nbroeking/Apollo/SongListener/src/Application.cpp

#include "ScopedLock.h"
#include "Event.h"
#include "Log.h"
#include "Application.h"
#include <fftw3.h>
#include <cstring>
#include <math.h>
#include <unistd.h>
#include "Processor.h"
using namespace std;

//Main Running Loop
int MainApplication::run()
{
	//No two threads can try and run the application at a time. It shouldn't
	// happen anyway but you never know what mistakes i will make.
	isRunning = true;
	
    if (!(s = pa_simple_new(NULL, "Song Listener", PA_STREAM_RECORD, NULL, "record", &ss, NULL, NULL, &error))) {
        fprintf(stderr, __FILE__": pa_simple_new() failed: %s\n", pa_strerror(error));
        return 2;
    }
	while (shouldRun.load())
	{
	    int16_t buf[BUFSIZE];
       
        
        //Record some data ...
        if (pa_simple_read(s, buf, sizeof(buf), &error) < 0) {
            fprintf(stderr, __FILE__": pa_simple_read() failed: %s\n", pa_strerror(error));
            return 3;
        }
 
        //THis is a bad check so we only do the fft on real data
        if( buf[0] != 0){
           
            //Combining the left and right streams
           for( int i = 0; i < INSIZE; i++){
                int16_t left = buf[i*2];
                int16_t right = buf[i*2 +1];

                in[i] = ((float)left + (float)right) / 65536.f;
            }

            //Windowing I think 
            for( int i =0; i < INSIZE; i++){
                //in[i] = buf[i];
                in[i] *= 0.54f - 0.46f * cosf( (3.1415926 * 2.f * i) / (BUFSIZE - 1) ); 
            }


            fftw_execute(p);

            // I rewrite to out[i][0] squared absolute value of a complex number out[i].
            //int step = MAXFREQ/OUTPUTSIZE;
            int steps = 1;

            int integral = 0;
            
            // cerr << "Values"<< endl;
            for (int i = 0; i < MAXANALYZE; ++i)
            {
                double value = out[i][0]*out[i][0] + out[i][1]*out[i][1];
                integral += value;
                //out[i][0] = 10*log(value);
                //out[i][0] = 10*log(value);
                out[i][0] = value;
                //cerr << steps*step << ", " << out[i][0]<< endl;
                steps+=1;
            }
            
            //ncerr << "Intgral, "<< integral << endl;           

            //exit(0);
            int8_t  bitmask[8];

            processor.process(out, MAXANALYZE, bitmask,integral);


            /*cout << "Bitmask" << endl;

            for( int i =0; i < 8; i++){
                printf(" 0x%02X ", bitmask[i] );
            }
            cout << endl;
            */
            if( arduino){
                fwrite(bitmask , sizeof(char), 8, arduino);
            }
            fflush(arduino);
          
             
            //exit(0);
        }
    }

	isRunning = false;

    printf("LIGHTD: Application Exiting Normally\n");
	return 0;
}

//Constructor
MainApplication::MainApplication(){
	isRunning = false;
	shouldRun.store(true);

    arduino = NULL;

    //Oh gods of programming Im sorry for this polling law break
    int retries = 0;
    while(access ("/dev/ttyACM0", F_OK) != 0)
    {
        fprintf(stderr, "Could not find the arduino trying again in 3 seconds\n");
        sleep(3);
        retries += 1;

       if( retries > 10){
            shouldRun.store(false);
            break;
        }
    }
    
   
    arduino = fopen("/dev/ttyACM0", "w");

    s = NULL;
   
   for (int i = 0; i < BUFSIZE; ++i){
        in[i] = 0.f;
    }
   for (int i = 0; i < OUTPUTSIZE; ++i){
        out[i][0] = 0.0;
        out[i][1] = 0.0;
    }
    p = fftw_plan_dft_r2c_1d(INSIZE, in, out, FFTW_ESTIMATE); 
}


MainApplication::~MainApplication()
{
    printf("LIGHTD: Shutting down the Main Application\n");
    if( arduino){
        fclose(arduino);
    }

    if( s != NULL){
        pa_simple_free(s);
        printf("LIGHTD: Successfully cleaned up the pulse audio library\n");
    }
    else{
        printf("LIGHTD: Application could not clean up pulse objects\n");
    }
    fftw_destroy_plan(p);
    fftw_cleanup();

    printf( "Succesfully cleaned up FFT library\n");
}
void MainApplication::pleaseDie()
{
	printf("LIGHTD: Asking the Main application to die\n");
    //Add a close event to the application
    shouldRun.store(false);
}
