nbroeking/Apollo/SongListener/src/Pin.cpp

#include <fstream>
#include <string>
#include <iostream>
#include <sstream>
#include "Pin.h"
#include "Log.h"
 
using namespace std;
 
Pin::Pin(string gnum)
{
	this->gpionum = gnum;  //Instatiate Pin object for GPIO pin number "gnum"
	isOn = false;
    export_gpio();
	setdir_gpio("out");
}

Pin::~Pin()
{
	unexport_gpio();
} 
int Pin::export_gpio()
{
    string export_str = "/sys/class/gpio/export";
    ofstream exportgpio(export_str.c_str()); // Open "export" file. Convert C++ string to C string. Required for all Linux pathnames
    if (exportgpio < 0){
        cout << "PiError: OPERATION FAILED: Unable to export GPIO"<< this->gpionum <<" ."<< endl;
        return -1;
    }
 
    exportgpio << this->gpionum ; //write GPIO number to export
    exportgpio.close(); //close export file
    return 0;
}
 
int Pin::unexport_gpio()
{
    string unexport_str = "/sys/class/gpio/unexport";
    ofstream unexportgpio(unexport_str.c_str()); //Open unexport file
    if (unexportgpio < 0){
        cout << "PiError: OPERATION FAILED: Unable to unexport GPIO"<< this->gpionum <<" ."<< endl;
        return -1;
    }
 
    unexportgpio << this->gpionum ; //write GPIO number to unexport
    unexportgpio.close(); //close unexport file
    return 0;
}
 
int Pin::setdir_gpio(string dir)
{
 
    string setdir_str ="/sys/class/gpio/gpio" + this->gpionum + "/direction";
    ofstream setdirgpio(setdir_str.c_str()); // open direction file for gpio
        if (setdirgpio < 0){
            cout << "PiError: OPERATION FAILED: Unable to set direction of GPIO"<< this->gpionum <<" ."<< endl;
            return -1;
        }
 
        setdirgpio << dir; //write direction to direction file
        setdirgpio.close(); // close direction file
        return 0;
}
 
int Pin::on()
{
    if( isOn){
       return 0 ;
    } 
    string setval_str = "/sys/class/gpio/gpio" + this->gpionum + "/value";
    ofstream setvalgpio(setval_str.c_str()); // open value file for gpio
        if (setvalgpio < 0){
            cout << "PiError: OPERATION FAILED: Unable to set the value of GPIO"<< this->gpionum <<" ."<< endl;
            return -1;
        }
 
        setvalgpio << "1" ;//write value to value file
        setvalgpio.close();// close value file 
        isOn = true;
        return 0;
}
 
int Pin::off()
{
    if( !isOn){
        return 0;
    }
    string setval_str = "/sys/class/gpio/gpio" + this->gpionum + "/value";
    ofstream setvalgpio(setval_str.c_str()); // open value file for gpio
        if (setvalgpio < 0){
            cout << "PiError: OPERATION FAILED: Unable to set the value of GPIO"<< this->gpionum <<" ."<< endl;
            return -1;
        }
 
        setvalgpio << "0" ;//write value to value file
        setvalgpio.close();// close value file 
        isOn = false;
        return 0;
}
int Pin::getval_gpio(string& val){
 
    string getval_str = "/sys/class/gpio/gpio" + this->gpionum + "/value";
    ifstream getvalgpio(getval_str.c_str());// open value file for gpio
    if (getvalgpio < 0){
        cout << "PiError: OPERATION FAILED: Unable to get value of GPIO"<< this->gpionum <<" ."<< endl;
        return -1;
            }
 
    getvalgpio >> val ;  //read gpio value
 
    if(val != "0")
        val = "1";
    else
        val = "0";
 
    getvalgpio.close(); //close the value file
    return 0;
}
 
string Pin::getVal(){
 
return this->gpionum;
 
}
